ogoudard/VO2max/Results/2026_01_28/Data_Example.jpeg

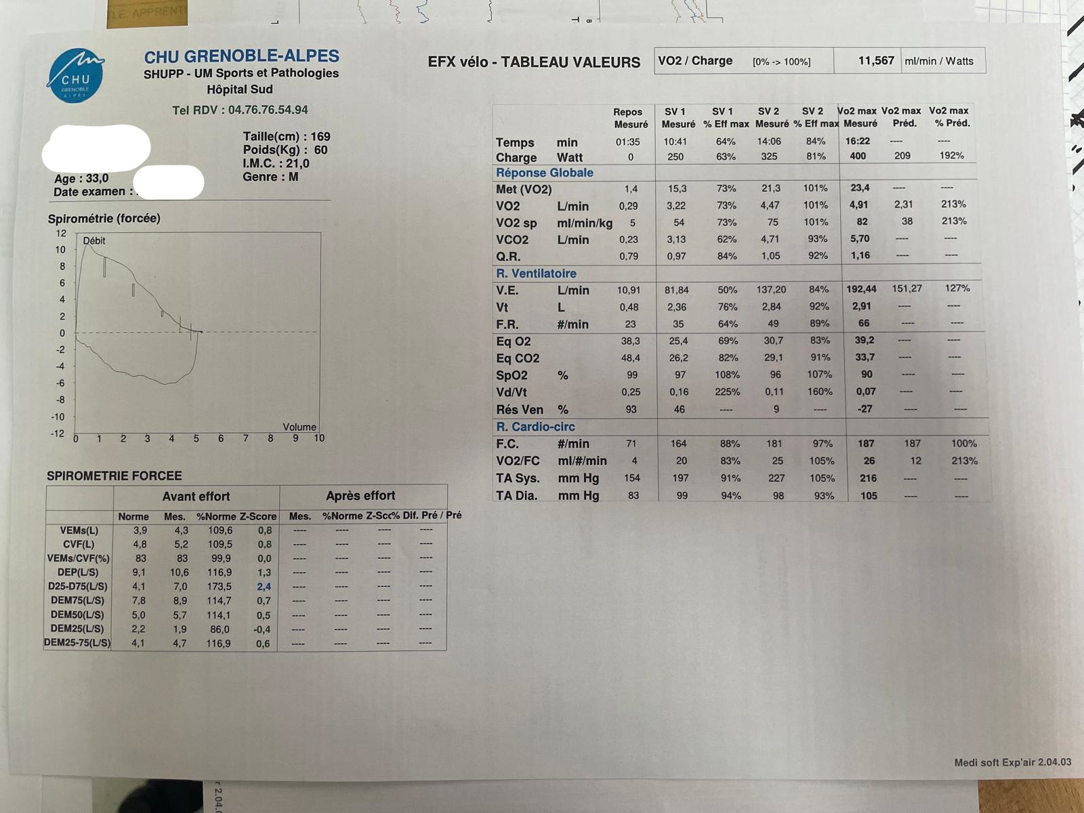
Results/2026_01_28/Data_Example.jpeg
