ogoudard/VO2max/Results/2026_01_28/Data_Example_2.jpeg

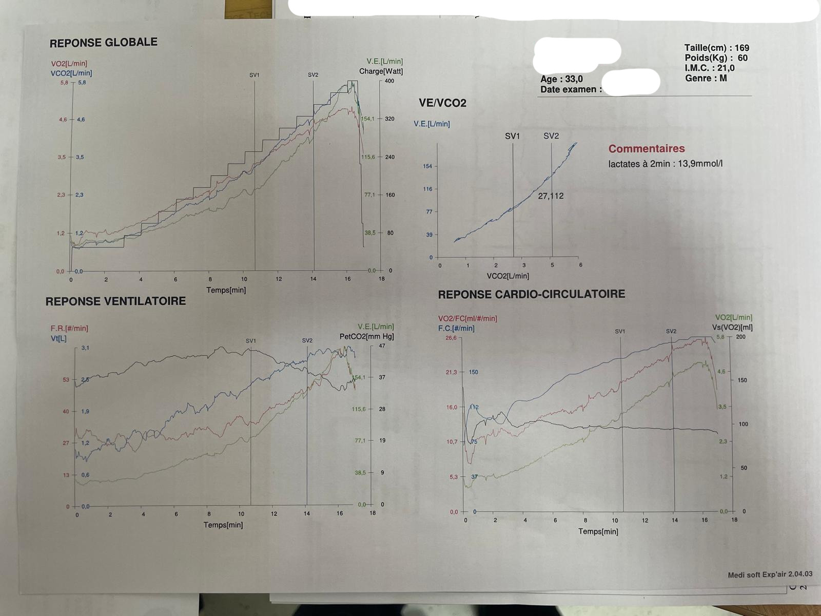
Results/2026_01_28/Data_Example_2.jpeg
