ogoudard/VO2max/CAD/TTGO_T_Display_Front_V2_0.STL

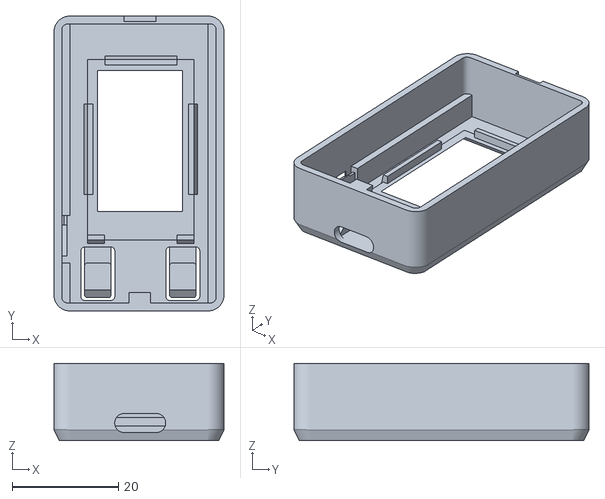
[picture p28: CAD file, 2026-04-22]
CAD/TTGO_T_Display_Front_V2_0.STL
32.0 x 55.5 x 14.5
