ogoudard/VO2max/CAD/Pompe3L/Piston.STL

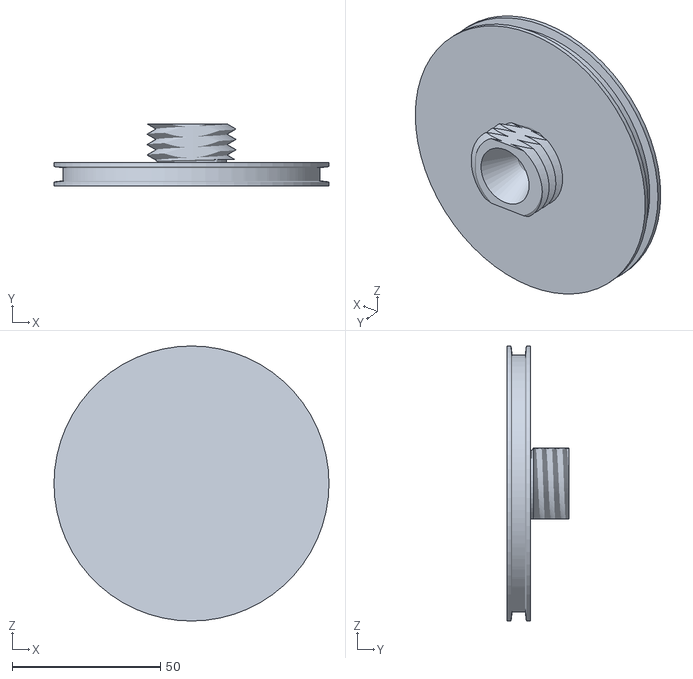
[picture p29: CAD file, 2026-02-27]
CAD/Pompe3L/Piston.STL
92.7 x 21.0 x 92.7
