ogoudard/VO2max/CAD/Pompe3L/Adaptateur_V1.STL

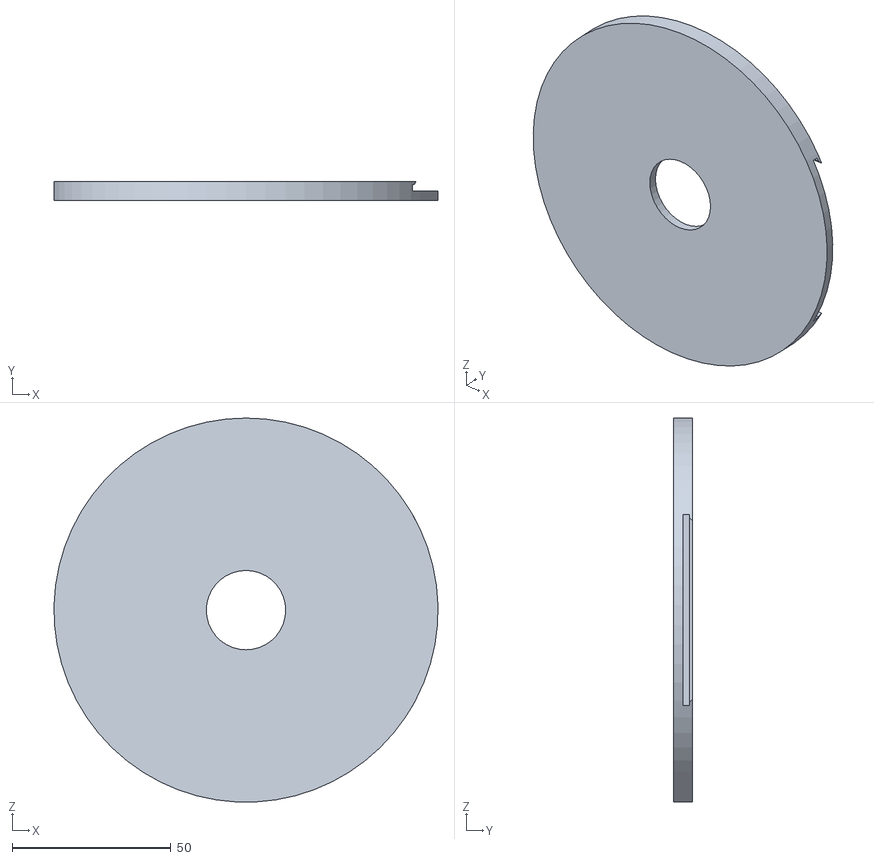
[picture p30: CAD file, 2026-02-27]
CAD/Pompe3L/Adaptateur_V1.STL
121.0 x 6.00 x 120.9
