ogoudard/VO2max/CAD/Pompe3L/Lock.STL

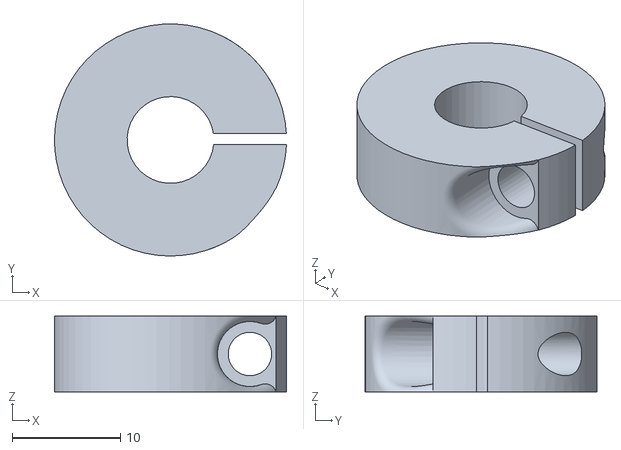
[picture p31: CAD file, 2026-02-27]
CAD/Pompe3L/Lock.STL
21.4 x 21.4 x 7.00
