ogoudard/VO2max/Embedded Software/VO2max/main/driver_st7789_font.h

#ifndef DRIVER_ST7789_FONT_H
#define DRIVER_ST7789_FONT_H

#include <stdint.h>
#include <stdio.h>
#include <string.h>

/**
 * @brief ascii 1206 definition
 */
static const uint8_t gsc_st7789_ascii_1206[95][12] =
    {
        {0x00, 0x00, 0x00, 0x00, 0x00, 0x00, 0x00, 0x00, 0x00, 0x00, 0x00, 0x00}, /*" ", 0*/
        {0x00, 0x00, 0x00, 0x00, 0x3F, 0x40, 0x00, 0x00, 0x00, 0x00, 0x00, 0x00}, /*"!", 1*/
        {0x00, 0x00, 0x30, 0x00, 0x40, 0x00, 0x30, 0x00, 0x40, 0x00, 0x00, 0x00}, /*""", 2*/
        {0x09, 0x00, 0x0B, 0xC0, 0x3D, 0x00, 0x0B, 0xC0, 0x3D, 0x00, 0x09, 0x00}, /*"#", 3*/
        {0x18, 0xC0, 0x24, 0x40, 0x7F, 0xE0, 0x22, 0x40, 0x31, 0x80, 0x00, 0x00}, /*"$", 4*/
        {0x18, 0x00, 0x24, 0xC0, 0x1B, 0x00, 0x0D, 0x80, 0x32, 0x40, 0x01, 0x80}, /*"%", 5*/
        {0x03, 0x80, 0x1C, 0x40, 0x27, 0x40, 0x1C, 0x80, 0x07, 0x40, 0x00, 0x40}, /*"&", 6*/
        {0x10, 0x00, 0x60, 0x00, 0x00, 0x00, 0x00, 0x00, 0x00, 0x00, 0x00, 0x00}, /*"'", 7*/
        {0x00, 0x00, 0x00, 0x00, 0x00, 0x00, 0x1F, 0x80, 0x20, 0x40, 0x40, 0x20}, /*"(", 8*/
        {0x00, 0x00, 0x40, 0x20, 0x20, 0x40, 0x1F, 0x80, 0x00, 0x00, 0x00, 0x00}, /*")", 9*/
        {0x09, 0x00, 0x06, 0x00, 0x1F, 0x80, 0x06, 0x00, 0x09, 0x00, 0x00, 0x00}, /*"*", 10*/
        {0x04, 0x00, 0x04, 0x00, 0x3F, 0x80, 0x04, 0x00, 0x04, 0x00, 0x00, 0x00}, /*"+", 11*/
        {0x00, 0x10, 0x00, 0x60, 0x00, 0x00, 0x00, 0x00, 0x00, 0x00, 0x00, 0x00}, /*", ", 12*/
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
        {0x00, 0x00, 0x00, 0x00, 0x3F, 0x80, 0x01, 0xFF, 0xE0, 0x03, 0x80, 0x70, 0x02, 0x00, 0x18, 0x04, 0x00, 0x08, 0x04, 0x00, 0x08, 0x04, 0x00, 0x08, 0x04, 0x00, 0x10, 0x06, 0x00, 0x20, 0x07, 0x80, 0xC0, 0x00, 0x00, 0x00}, /*"C", 35*/
        {0x04, 0x00, 0x08, 0x07, 0xFF, 0xF8, 0x07, 0xFF, 0xF8, 0x04, 0x00, 0x08, 0x04, 0x00, 0x08, 0x04, 0x00, 0x08, 0x04, 0x00, 0x18, 0x02, 0x00, 0x10, 0x03, 0x80, 0x70, 0x01, 0xFF, 0xE0, 0x00, 0x7F, 0x80, 0x00, 0x00, 0x00}, /*"D", 36*/
        {0x04, 0x00, 0x08, 0x07, 0xFF, 0xF8, 0x07, 0xFF, 0xF8, 0x04, 0x08, 0x08, 0x04, 0x08, 0x08, 0x04, 0x08, 0x08, 0x04, 0x08, 0x08, 0x04, 0x3E, 0x08, 0x04, 0x00, 0x08, 0x06, 0x00, 0x18, 0x01, 0x00, 0x60, 0x00, 0x00, 0x00}, /*"E", 37*/
        {0x04, 0x00, 0x08, 0x07, 0xFF, 0xF8, 0x07, 0xFF, 0xF8, 0x04, 0x08, 0x08, 0x04, 0x08, 0x00, 0x04, 0x08, 0x00, 0x04, 0x08, 0x00, 0x04, 0x3E, 0x00, 0x06, 0x00, 0x00, 0x06, 0x00, 0x00, 0x01, 0x80, 0x00, 0x00, 0x00, 0x00}, /*"F", 38*/
        {0x00, 0x00, 0x00, 0x00, 0x3F, 0x80, 0x01, 0xFF, 0xE0, 0x03, 0x80, 0x70, 0x06, 0x00, 0x18, 0x04, 0x00, 0x08, 0x04, 0x02, 0x08, 0x04, 0x02, 0x08, 0x02, 0x03, 0xF0, 0x07, 0x83, 0xF0, 0x00, 0x02, 0x00, 0x00, 0x02, 0x00}, /*"G", 39*/
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
};

#endif
