ogoudard/VO2max/Embedded Software/VO2max/main/driver_me2o2.h

#ifndef __DRIVER_ME2O2_H__
#define __DRIVER_ME2O2_H__

#include "driver/i2c_master.h"

#define ME2O2_I2C_ADDRESS_0x70 0x70
#define ME2O2_I2C_ADDRESS_0x71 0x71
#define ME2O2_I2C_ADDRESS_0x72 0x72
#define ME2O2_I2C_ADDRESS_0x73 0x73

bool ME2O2_Initialize(i2c_master_bus_handle_t i2cBusHandle, uint8_t address);
void ME2O2_Calibrate(float vol);
bool ME2O2_ReadOxygen(float *oxygen);

#endif /* __DRIVER_ME2O2_H__ */
