ogoudard/VO2max/Embedded Software/VO2max/main/cyclist_vo2max_rgb565.h

#ifndef CYCLIST_VO2MAX_RGB565_H
#define CYCLIST_VO2MAX_RGB565_H

#include <stdint.h>

#define CYCLIST_WIDTH 240
#define CYCLIST_HEIGHT 135

/* RGB565 image data, 32400 pixels, row-major */
static const uint16_t cyclist_image[32400] = {
    0x6BB2, 0x6BD2, 0x6BD2, 0x6BD2, 0x73F2, 0x73F2, 0x73F2, 0x73F2,
    0x73F2, 0x7412, 0x73F2, 0x73F2, 0x6BF2, 0x6BF2, 0x6BD2, 0x6BD2,
    0x6BD1, 0x6BD1, 0x6BD1, 0x6BD1, 0x6BD2, 0x6BF2, 0x6BF2, 0x6BF2,
    0x6BF2, 0x7413, 0x7413, 0x7413, 0x7433, 0x7433, 0x7433, 0x7454,
    0x7454, 0x7C54, 0x7C54, 0x7C74, 0x7C75, 0x8474, 0x8474, 0x8495,
    0x8495, 0x84B5, 0x84B5, 0x84B5, 0x84B5, 0x84B5, 0x8CB5, 0x84B5,
    0x84B5, 0x84B5, 0x84B5, 0x84B5, 0x84B5, 0x84B5, 0x84B5, 0x84B5,
    0x84B5, 0x84B5, 0x8495, 0x8495, 0x7C74, 0x7C74, 0x7C54, 0x7C54,
    0x7433, 0x7433, 0x7433, 0x7433, 0x7433, 0x7433, 0x7433, 0x7433,
    0x7433, 0x7453, 0x7C74, 0x7C74, 0x7C95, 0x8495, 0x8495, 0x8495,
    0x8495, 0x8495, 0x8495, 0x8495, 0x8495, 0x8495, 0x84B5, 0x84B5,
    0x84B5, 0x8CB5, 0x8CD5, 0x8CD5, 0x8CB5, 0x84B5, 0x84B5, 0x84B5,
    0x8CB5, 0x8CD5, 0x8CD5, 0x8CB5, 0x8494, 0x8473, 0x7C33, 0x7432,
    0x7412, 0x73F1, 0x6BD1, 0x6BB0, 0x6370, 0x636F, 0x5B4F, 0x5B4F,
    0x5B4F, 0x634F, 0x636F, 0x636F, 0x636F, 0x636F, 0x6390, 0x6390,
    0x6390, 0x6B90, 0x6BB1, 0x6BD1, 0x6BD1, 0x6BD1, 0x6BD1, 0x73D1,
    0x6BD1, 0x73F1, 0x5B0C, 0x49C6, 0x6AAA, 0x528A, 0x4A69, 0x4A28,
    0x7187, 0x20C2, 0x0820, 0x3185, 0x41E7, 0x1081, 0x39A5, 0x3165,
    0x2103, 0x20E3, 0x3164, 0x3144, 0x18A2, 0x0841, 0x0840, 0x0841,
    0x1061, 0x3165, 0x3144, 0x18C2, 0x18A2, 0x20C2, 0x18A2, 0x1061,
    0x1061, 0x0840, 0x0820, 0x0820, 0x0820, 0x0020, 0x1061, 0x20C2,
    0x28E2, 0x5227, 0x4A27, 0x4A28, 0x62EC, 0x634E, 0x6B6F, 0x632D,
    0x632D, 0x634F, 0x5B2E, 0x632E, 0x632E, 0x5B2E, 0x5B2E, 0x5B2E,
    0x5B2E, 0x5B2E, 0x5B2E, 0x5B2E, 0x5B2E, 0x5B2E, 0x5B0D, 0x5B0D,
    0x5B0E, 0x52ED, 0x52ED, 0x52CD, 0x52ED, 0x52CD, 0x52CD, 0x52CD,
    0x52ED, 0x5B0D, 0x5B0D, 0x630E, 0x632E, 0x634E, 0x632E, 0x5B0D,
    0x5B0D, 0x5AED, 0x5AED, 0x5AED, 0x52ED, 0x52ED, 0x52ED, 0x52ED,
    0x5AED, 0x5AED, 0x5AED, 0x5B0D, 0x5B0D, 0x632E, 0x632E, 0x634E,
    0x634E, 0x6B4E, 0x6B4E, 0x6B6E, 0x6B6E, 0x6B6E, 0x6B6F, 0x6B6E,
    0x634E, 0x634E, 0x634E, 0x634E, 0x632D, 0x5B0D, 0x5AEC, 0x52CC,
    0x63B1, 0x6BB2, 0x6BD2, 0x73F2, 0x73F2, 0x73F2, 0x73F2, 0x7412,
    0x73F2, 0x7412, 0x7412, 0x73F2, 0x73F2, 0x6BF2, 0x6BF2, 0x6BD2,
    0x6BD1, 0x6BD1, 0x6BD1, 0x6BD1, 0x6BD2, 0x6BD2, 0x6BF2, 0x6BF2,
    0x6BF2, 0x6BF2, 0x6BF2, 0x6BF3, 0x6C13, 0x7413, 0x7433, 0x7433,
    0x7433, 0x7454, 0x7454, 0x7C54, 0x7C74, 0x7C74, 0x7C74, 0x8474,
    0x8494, 0x8495, 0x84B5, 0x84B5, 0x84B5, 0x8CB5, 0x8CB5, 0x84B6,
    0x84B5, 0x84B5, 0x84B5, 0x84B5, 0x84B5, 0x8495, 0x84B5, 0x84B5,
    0x84B5, 0x84B5, 0x8495, 0x8474, 0x7C74, 0x7C54, 0x7434, 0x7433,
    0x7433, 0x7433, 0x7413, 0x7413, 0x7433, 0x7433, 0x7433, 0x7433,
    0x7453, 0x7C54, 0x7C54, 0x7C74, 0x7C95, 0x8495, 0x8495, 0x8495,
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

#endif
