ogoudard/VO2max/Embedded Software/VO2max/main/measure.h

#ifndef __MEASURE_H__
#define __MEASURE_H__

#include "freertos/FreeRTOS.h"
#include "freertos/queue.h"

extern QueueHandle_t g_instantFlowQueue;
extern QueueHandle_t g_o2Queue;
extern QueueHandle_t g_co2Queue;
extern QueueHandle_t g_temperatureQueue;
extern QueueHandle_t g_humidityQueue;
extern QueueHandle_t g_totalExhaledVolumeQueue;
extern QueueHandle_t g_cycleExhaledVolumeQueue;
extern QueueHandle_t g_pressureQueue;
extern QueueHandle_t g_altitudeQueue;
extern QueueHandle_t g_respiratoryRateQueue;
extern QueueHandle_t g_vO2Queue;
extern QueueHandle_t g_vO2MaxQueue;
extern QueueHandle_t g_vCo2Queue;
extern QueueHandle_t g_respiratoryQuotientQueue;
extern QueueHandle_t g_o2CalibrationQueue;
extern QueueHandle_t g_expiratoryFlowQueue;

extern SemaphoreHandle_t g_flowInitializationSemaphore;
extern SemaphoreHandle_t g_o2InitializationSemaphore;
extern SemaphoreHandle_t g_co2InitializationSemaphore;
extern SemaphoreHandle_t g_pressureInitializationSemaphore;
extern SemaphoreHandle_t g_resetExhaledVolumeSemaphore;
extern SemaphoreHandle_t g_resetVo2MaxSemaphore;

void MEASURE_Initialize(void);

#endif
