ogoudard/VO2max/Embedded Software/VO2max/main/plot.c

#include "plot.h"
#include "driver/uart.h"
#include "esp_timer.h"

#define UART_NUM_DEBUG UART_NUM_1
#define START_BYTE 0xAA

typedef union
{
    double value;
    uint8_t bytes[8];
} DoubleValue_u;

QueueHandle_t uartQueue;

void PLOT_Initialize(void)
{
    ESP_ERROR_CHECK(uart_driver_install(UART_NUM_DEBUG, 1024, 1024, 10, &uartQueue, 0));
}

void PLOT_SendData(uint8_t id, double value)
{
    uint8_t buffer[18];
    uint8_t *ts;
    DoubleValue_u d;
    int64_t timestamp;

    timestamp = esp_timer_get_time();

    d.value = value;

    buffer[0] = START_BYTE;
    buffer[1] = id;

    // float32
    for (uint8_t i = 0; i < sizeof(d.value); i++)
    {
        buffer[2 + i] = d.bytes[i];
    }

    // int64_t timestamp (raw bytes, little-endian ESP32)
    ts = (uint8_t *)&timestamp;

    for (int i = 0; i < 8; i++)
    {
        buffer[10 + i] = ts[i];
    }

    uart_write_bytes(UART_NUM_DEBUG, (const void *)buffer, sizeof(buffer));
}
