ogoudard/VO2max/Embedded Software/VO2max/main/menu.h

#ifndef __MENU_H__
#define __MENU_H__

#include "stdint.h"

#define MAX_MENU_SIZE 10
#define MAX_MENU_NAME_SIZE 20

typedef void (*MenuAction_t)(void);

typedef struct Menu
{
    char name[MAX_MENU_NAME_SIZE + 1];
    struct Menu *parent;
    struct Menu *children[MAX_MENU_SIZE];
    uint8_t childrenCount;
    MenuAction_t action;
} Menu_t;

void MENU_Create(Menu_t *menu, const char *name);
void MENU_AddSubmenu(Menu_t *menu, Menu_t *submenu);
void MENU_AddAction(Menu_t *menu, MenuAction_t action);

#endif
